Niels-Clayton/self-tuning-buck-converter/Reports/Final Report/appendix/source_code.tex

\chapter{Source Code} \label{A:code}

\section*{Single Header Libraries: Hardware Drivers} \label{A:headers}

\subsection*{adc.h} \label{A:adc_code}
\lstinputlisting{code/adc.h} 

\newpage
\subsection*{pid.h} \label{A:pid_code}
\lstinputlisting{code/pid.h}

\newpage
\subsection*{pwm.h} \label{A:pwm_code}
\lstinputlisting{code/pwm.h}

\newpage
\section*{Application Code} \label{A:application_code}

\subsection*{buck\_converter.h}\label{A:buck_code}
\lstinputlisting{code/buck_converter.h} 

\newpage
\subsection*{buck\_converter.c}
\lstinputlisting{code/buck_coverter.c} 

\newpage
\subsection*{main.c} \label{A:main_code}
\lstinputlisting{code/main.c}
