Niels-Clayton/self-tuning-buck-converter/self-tuning-buck-converter/Peak Detector/Evaluation/error/final_design_error.pdf

Final Design
Measured Output Error vs Switching Frequency

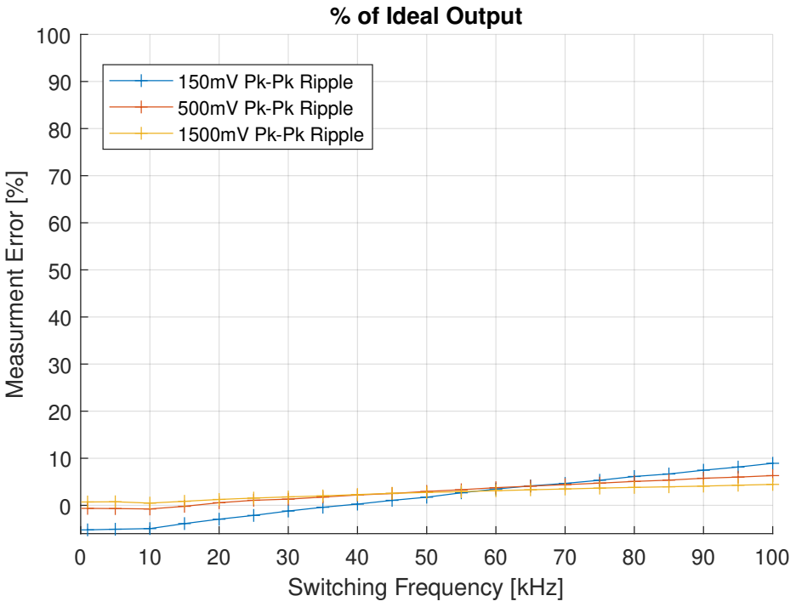
[picture p42: figure]
Switching Frequency [kHz]; Measurment Error [%]; % of Ideal Output; 150mV Pk-Pk Ripple 500mV Pk-Pk Ripple 1500mV Pk-Pk Ripple
