Niels-Clayton/self-tuning-buck-converter/docs/Planning/Proposal_Gantt_Chart.xlsx

ENGR489 Gantt Chart
Niels Clayton - Self Tuning Buck Converter
Month | March |  | April |  |  |  | May |  |  |  |  | June |  |  |  | July |  |  |  | August |  |  |  |  | September |  |  |  | October
Week Beginning | 22 | 29 | 5 | 12 | 19 | 26 | 3 | 10 | 17 | 24 | 31 | 7 | 14 | 21 | 28 | 5 | 12 | 19 | 26 | 2 | 9 | 16 | 23 | 30 | 6 | 13 | 20 | 27 | 4 | 11
Phase 1 - Research & Setup
Literature Review
Component Selection/Purchase
Buck Converter Dev Board Design
Phase 2 - Design
PWM Generation Testing & Evaluation
Feedback Sensor Testing & Evaluation
Complete Hardware Selection
Phase 3 - Implementation
Controller Implementation
Final PCB Design
Evaluation
Reports
Preliminary Report Writing
Presentation Preperation
Final Report Writing
Deadlines |  |  |  |  |  |  |  |  | Prelim. Report - 24/05 |  |  |  |  |  | Mid Year Break |  |  |  |  |  |  |  |  | Draft Final Report - 03/09 |  |  |  |  | Final Report - 08/10
 |  |  |  |  |  |  |  |  |  |  |  |  |  |  |  |  |  |  |  |  |  |  |  |  |  |  |  |  |  | Presentations - 15/10
