Niels-Clayton/self-tuning-buck-converter/Reports/Final Report/Figures/background/Duty_cycle.png

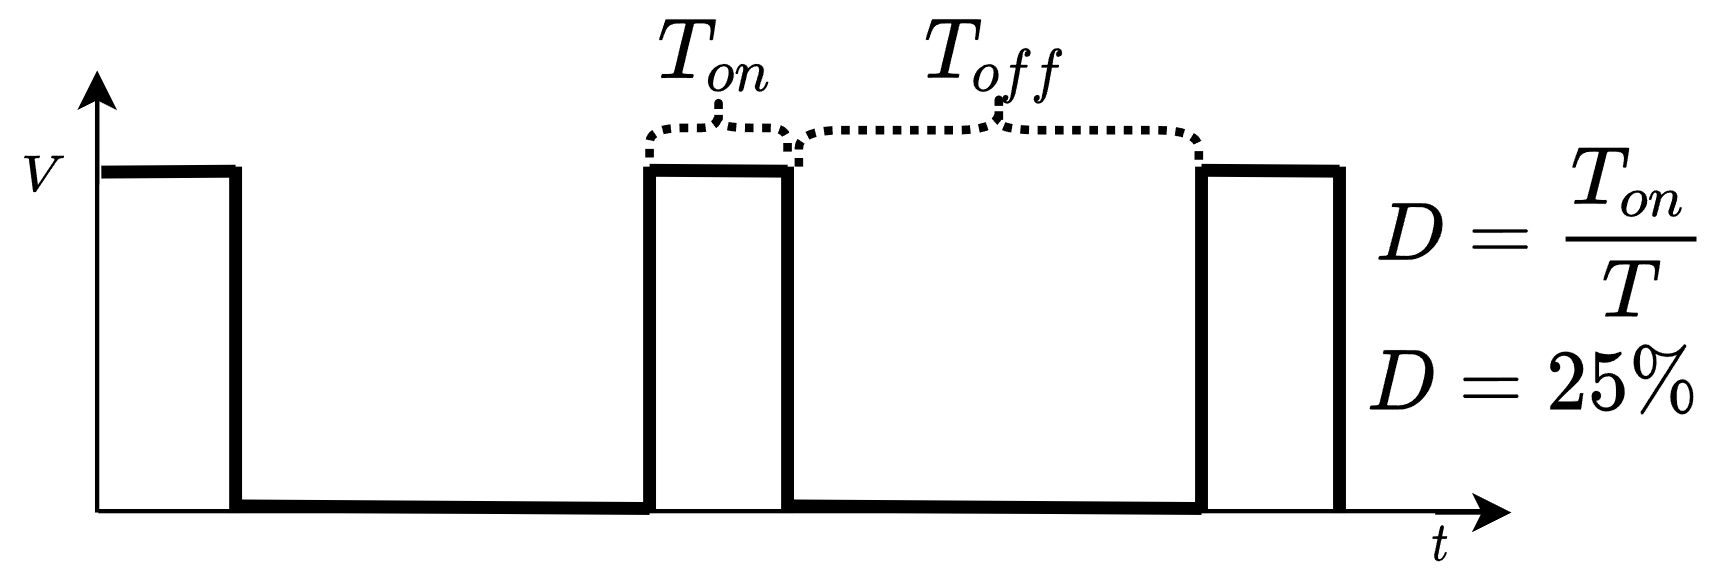
Reports/Final Report/Figures/background/Duty_cycle.png
