Niels-Clayton/self-tuning-buck-converter/Reports/Final Report/Figures/pwm/analog/analogue_PWM_ltspice_1k.png

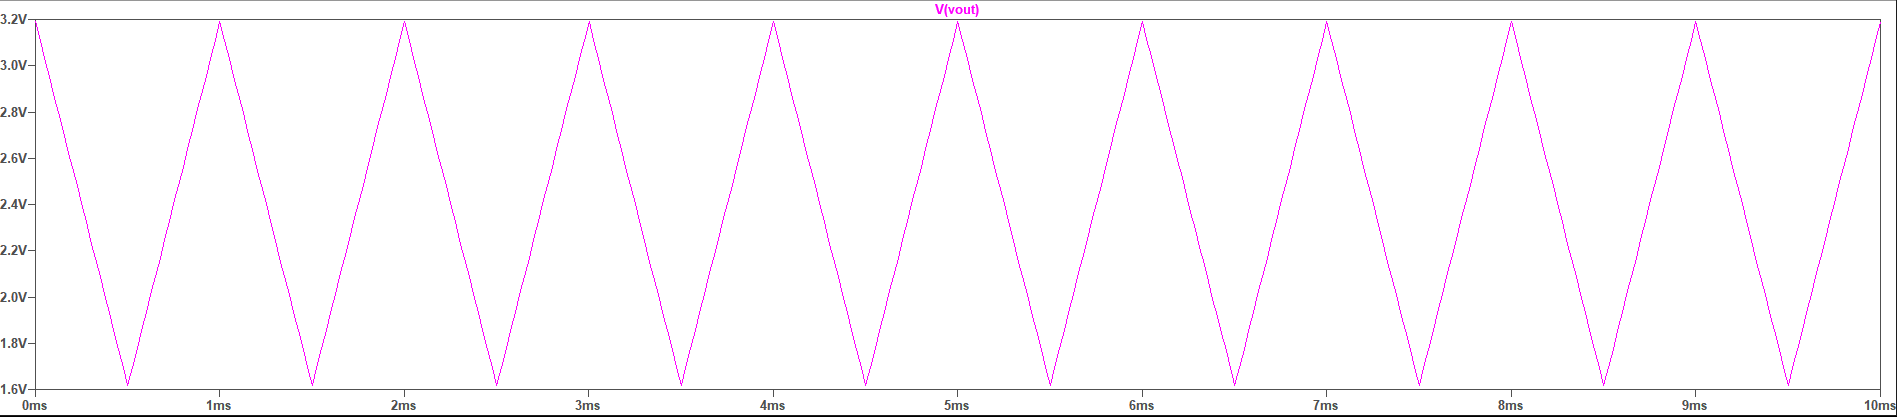
Reports/Final Report/Figures/pwm/analog/analogue_PWM_ltspice_1k.png
