Niels-Clayton/self-tuning-buck-converter/Reports/Final Report/Figures/pwm/duty/1kHz_75Duty.JPG

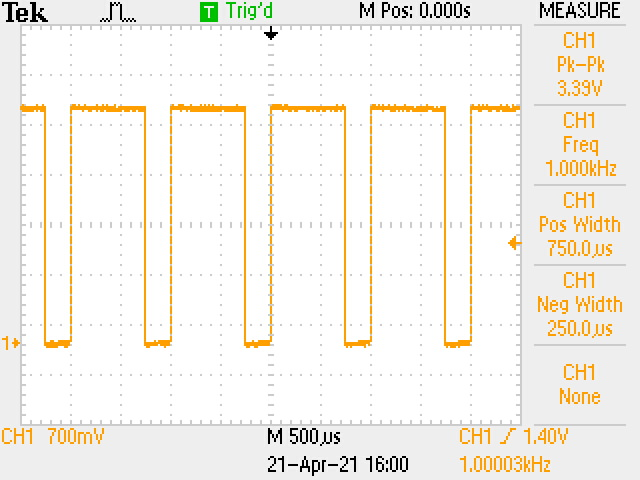
Reports/Final Report/Figures/pwm/duty/1kHz_75Duty.JPG
