Niels-Clayton/self-tuning-buck-converter/Reports/Final Report/Figures/pwm/duty/100kHz_50Duty.JPG

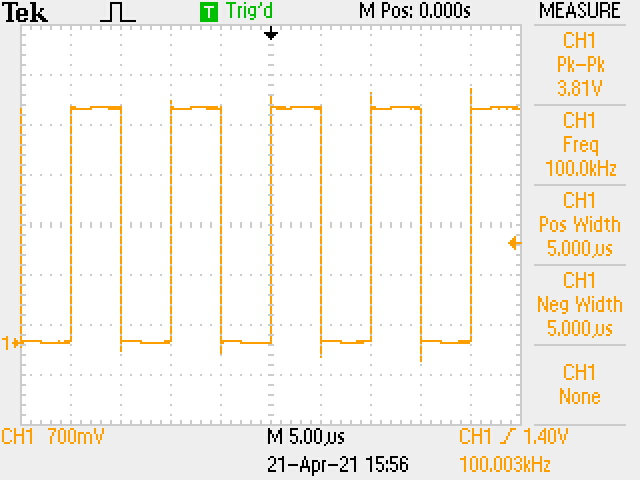
Reports/Final Report/Figures/pwm/duty/100kHz_50Duty.JPG
