Niels-Clayton/self-tuning-buck-converter/Reports/Final Report/Figures/pwm/duty/100kHz_75Duty.JPG

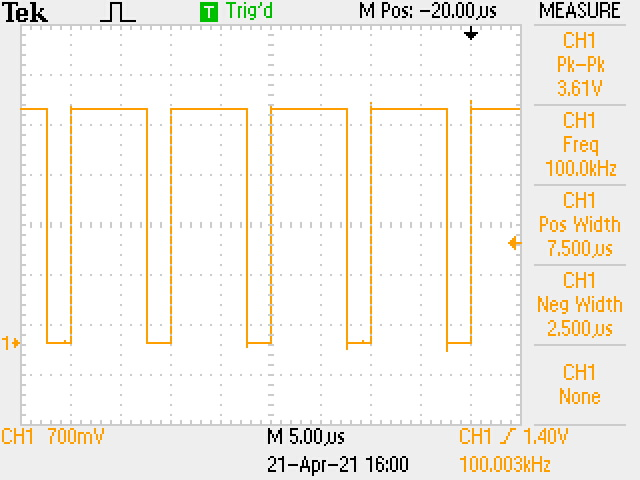
Reports/Final Report/Figures/pwm/duty/100kHz_75Duty.JPG
