Niels-Clayton/self-tuning-buck-converter/Reports/Final Report/Figures/control/step_response/voltage_control_3-10-0.PNG

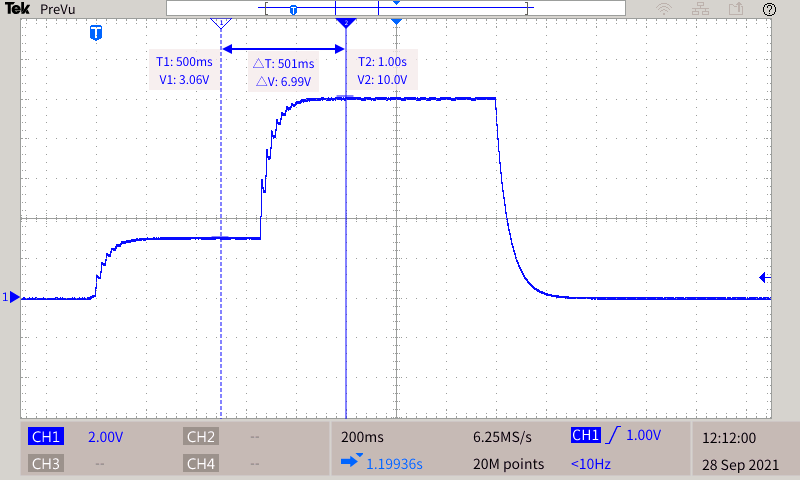
Reports/Final Report/Figures/control/step_response/voltage_control_3-10-0.PNG
