Niels-Clayton/self-tuning-buck-converter/self-tuning-buck-converter/Peak Detector/Evaluation/Peak Detector Evaluation.csv

Peak Detection Accuracy Comparison |  |  |  |  |  |  | Peak Detection Accuracy Comparison |  |  |  |  |  |  | Peak Detection Accuracy Comparison
Voltage pk-pk (mV) |  | 150 |  |  |  |  | Voltage pk-pk (mV) |  | 500 |  |  |  |  | Voltage pk-pk (mV) |  | 1500
Voltage Peak (mV) |  | 75 |  |  |  |  | Voltage Peak (mV) |  | 250 |  |  |  |  | Voltage Peak (mV) |  | 750
Voltage Refrence (mV) |  | 5999.90 |  |  |  |  | Voltage Refrence (mV) |  | 6002.20 |  |  |  |  | Voltage Refrence (mV) |  | 6001.70
Frequency (kHz) | V_out new (mV) | new error (mV) | new % error | V_out old (mV) | old error (mV) | old % error | Frequency (kHz) | V_out new (mV) | new error (mV) | new % error | V_out old (mV) | old error (mV) | old % error | Frequency (kHz) | V_out new (mV) | new error (mV) | new % error | V_out old (mV) | old error (mV) | old % error
1 | 6078.80 | -3.90 | -5.2 | 6071.50 | 3.40 | 4.533333333 | 1 | 6253.80 | -1.60 | -0.64 | 6245.20 | 7.00 | 2.8 | 1 | 6746.30 | 5.40 | 0.72 | 6736.70 | 15.00 | 2
5 | 6078.70 | -3.80 | -5.066666667 | 6069.10 | 5.80 | 7.733333333 | 5 | 6253.90 | -1.70 | -0.68 | 6237.20 | 15.00 | 6 | 5 | 6746.00 | 5.70 | 0.76 | 6722.00 | 29.70 | 3.96
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
