Niels-Clayton/self-tuning-buck-converter/self-tuning-buck-converter/PWM/evaluation/pwm_duty.csv

Actual | Target
0.996094 | 0.000000
0.996094 | 0.001953
0.000000 | 0.003906
0.500000 | 0.005859
0.500000 | 0.007812
0.750000 | 0.009766
0.800000 | 0.011719
0.800000 | 0.013672
0.857143 | 0.015625
0.875000 | 0.017578
0.875000 | 0.019531
0.900000 | 0.021484
0.900000 | 0.023438
0.916667 | 0.025391
0.923077 | 0.027344
0.923077 | 0.029297
0.933333 | 0.031250
0.937500 | 0.033203
0.937500 | 0.035156
0.944444 | 0.037109
0.947368 | 0.039062
0.947368 | 0.041016
0.952381 | 0.042969
0.954545 | 0.044922
0.954545 | 0.046875
0.958333 | 0.048828
0.958333 | 0.050781
0.961538 | 0.052734
0.962963 | 0.054688
0.962963 | 0.056641
0.965517 | 0.058594
0.966667 | 0.060547
0.966667 | 0.062500
0.968750 | 0.064453
0.969697 | 0.066406
0.969697 | 0.068359
0.971429 | 0.070312
0.971429 | 0.072266
0.972973 | 0.074219
0.973684 | 0.076172
0.973684 | 0.078125
0.975000 | 0.080078
0.975610 | 0.082031
0.975610 | 0.083984
0.976744 | 0.085938
0.977273 | 0.087891
0.977273 | 0.089844
0.978261 | 0.091797
0.978261 | 0.093750
0.979167 | 0.095703
0.979592 | 0.097656
0.979592 | 0.099609
0.980392 | 0.101562
0.980769 | 0.103516
0.980769 | 0.105469
0.981481 | 0.107422
0.981818 | 0.109375
0.981818 | 0.111328
0.982456 | 0.113281
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
