Niels-Clayton/self-tuning-buck-converter/self-tuning-buck-converter/PWM/evaluation/pwm_frequency.csv

Actual | Target | error | 62
1000 | 1000 | 0
1001 | 1001 | 0
1002 | 1002 | 0
1003 | 1003 | 0
1004 | 1004 | 0
1005 | 1005 | 0
1006 | 1006 | 0
1007 | 1007 | 0
1008 | 1008 | 0
1009 | 1009 | 0
1010 | 1010 | 0
1011 | 1011 | 0
1012 | 1012 | 0
1013 | 1013 | 0
1014 | 1014 | 0
1015 | 1015 | 0
1016 | 1016 | 0
1017 | 1017 | 0
1018 | 1018 | 0
1019 | 1019 | 0
1020 | 1020 | 0
1021 | 1021 | 0
1022 | 1022 | 0
1023 | 1023 | 0
1024 | 1024 | 0
1025 | 1025 | 0
1026 | 1026 | 0
1027 | 1027 | 0
1028 | 1028 | 0
1029 | 1029 | 0
1030 | 1030 | 0
1031 | 1031 | 0
1032 | 1032 | 0
1033 | 1033 | 0
1034 | 1034 | 0
1035 | 1035 | 0
1036 | 1036 | 0
1037 | 1037 | 0
1038 | 1038 | 0
1039 | 1039 | 0
1040 | 1040 | 0
1041 | 1041 | 0
1042 | 1042 | 0
1043 | 1043 | 0
1044 | 1044 | 0
1045 | 1045 | 0
1046 | 1046 | 0
1047 | 1047 | 0
1048 | 1048 | 0
1049 | 1049 | 0
1050 | 1050 | 0
1051 | 1051 | 0
1052 | 1052 | 0
1053 | 1053 | 0
1054 | 1054 | 0
1055 | 1055 | 0
1056 | 1056 | 0
1057 | 1057 | 0
1058 | 1058 | 0
1059 | 1059 | 0
1060 | 1060 | 0
1061 | 1061 | 0
1062 | 1062 | 0
1063 | 1063 | 0
1064 | 1064 | 0
1065 | 1065 | 0
1066 | 1066 | 0
1067 | 1067 | 0
1068 | 1068 | 0
1069 | 1069 | 0
1070 | 1070 | 0
1071 | 1071 | 0
1072 | 1072 | 0
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
