Niels-Clayton/self-tuning-buck-converter/self-tuning-buck-converter/Voltage_control_system/images/buck_closedloop_continuious.png

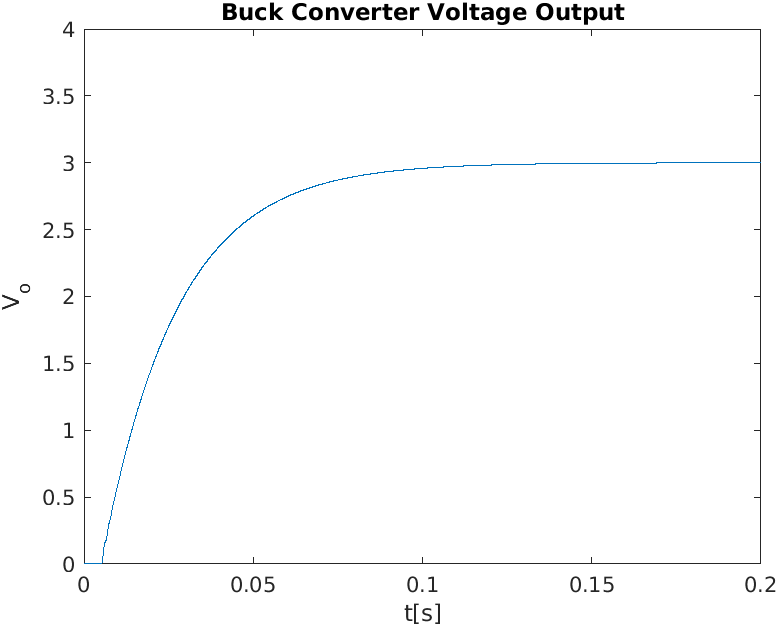
self-tuning-buck-converter/Voltage_control_system/images/buck_closedloop_continuious.png
