Niels-Clayton/self-tuning-buck-converter/self-tuning-buck-converter/Voltage_control_system/images/buck_controlled_discrete.png

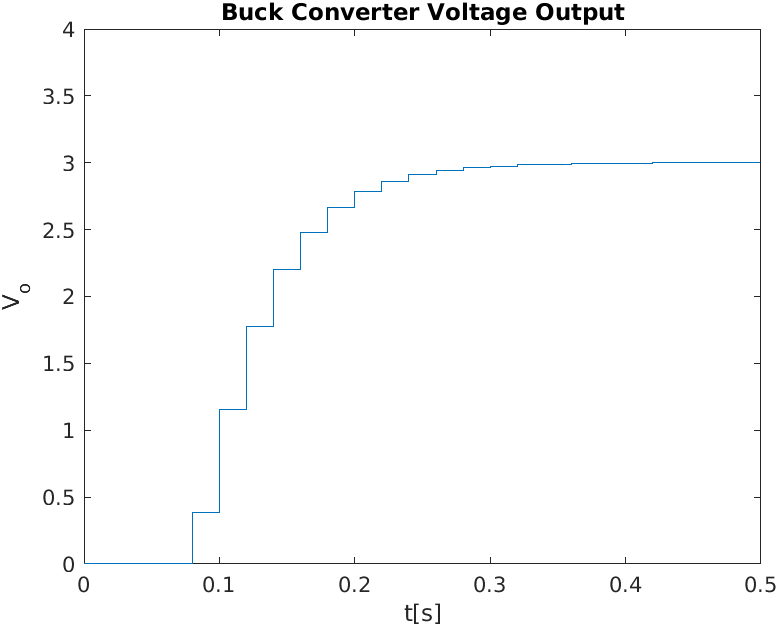
self-tuning-buck-converter/Voltage_control_system/images/buck_controlled_discrete.png
