Niels-Clayton/self-tuning-buck-converter/self-tuning-buck-converter/Voltage_control_system/images/buck_openloop_continuious.png

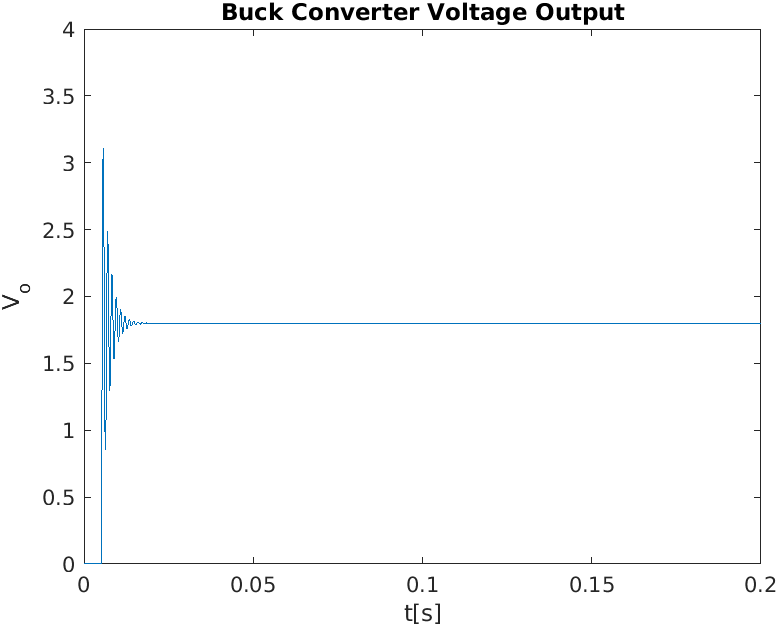
self-tuning-buck-converter/Voltage_control_system/images/buck_openloop_continuious.png
