Niels-Clayton/self-tuning-buck-converter/self-tuning-buck-converter/Voltage_control_system/images/closed_loop_voltage_out.png

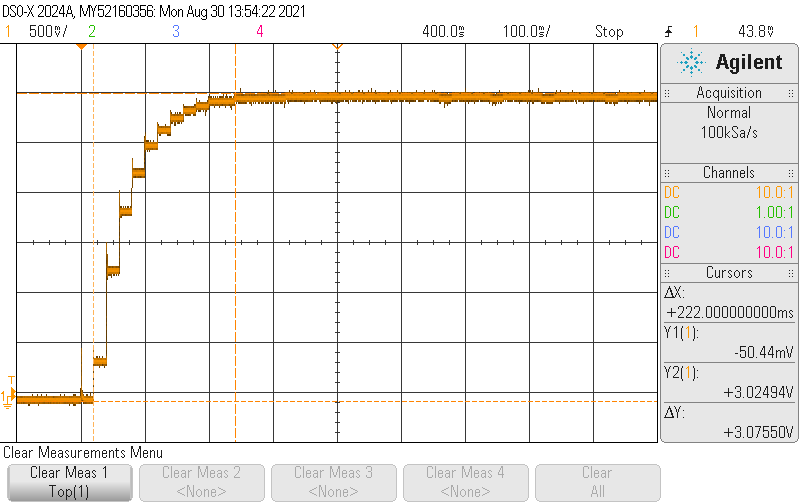
self-tuning-buck-converter/Voltage_control_system/images/closed_loop_voltage_out.png
