Niels-Clayton/self-tuning-buck-converter/self-tuning-buck-converter/Voltage_control_system/images/open_loop_votage_out.png

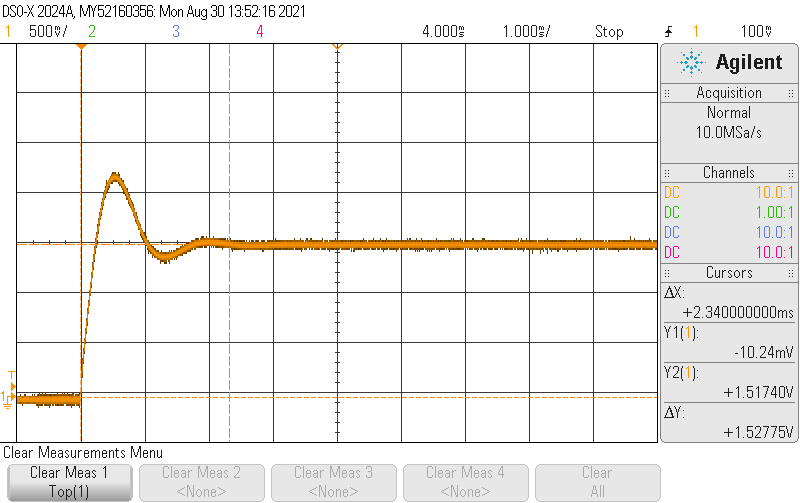
self-tuning-buck-converter/Voltage_control_system/images/open_loop_votage_out.png
