Niels-Clayton/self-tuning-buck-converter/Reports/Final Report/Figures/current_sense/schematic/average_current.pdf

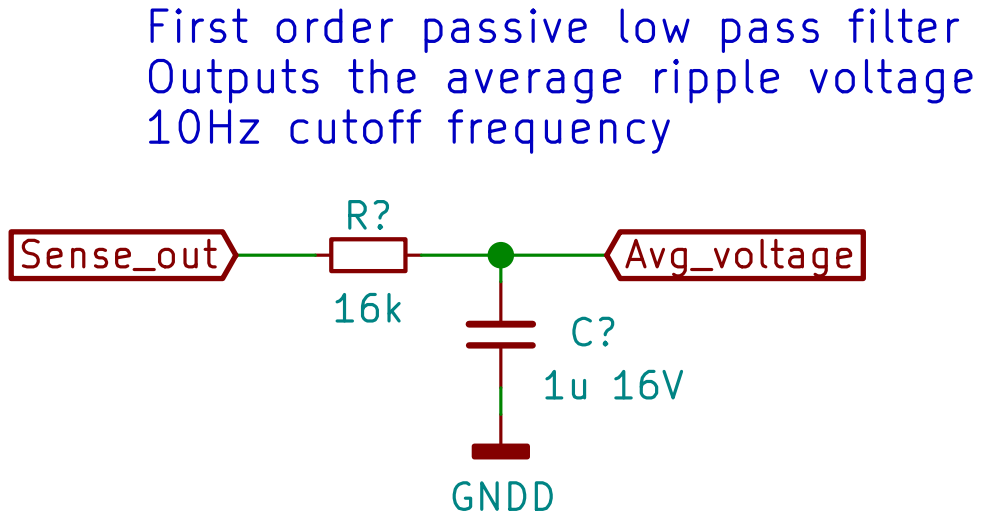
[picture p83: page 1]
GNDD; Avg_voltage V_ref; Pk_voltage; Sense_out Pk_voltage V_ref V_ref V_ref Sense_ripple; V_ref

First order passive low pass filter
Outputs the average ripple voltage
10Hz cutoff frequency

Id: 2/2 Title: File: test.sch Sheet: /test/ D? DIODE R?
