Niels-Clayton/self-tuning-buck-converter/Reports/Final Report/Figures/current_sense/schematic/precision_rectifier_schematic.pdf

3 | U?A OPAMP R?
3 | U?A OPAMP R?

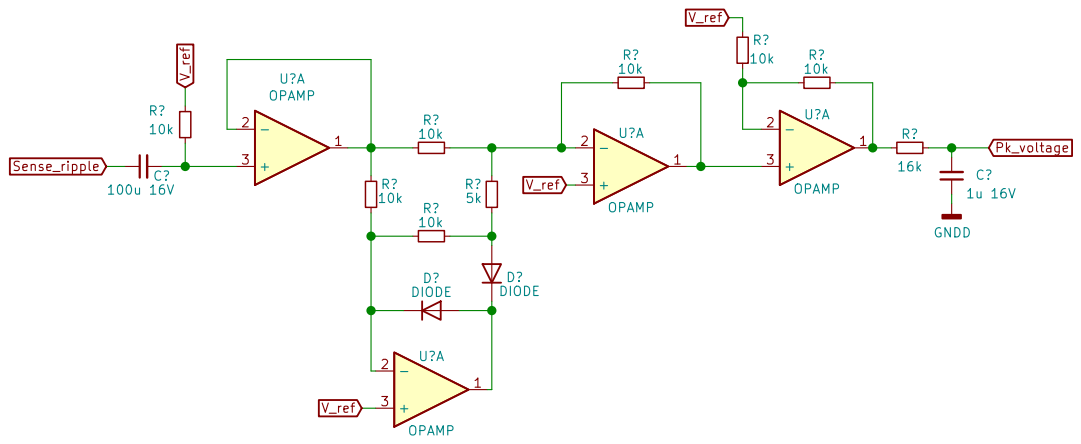
[picture p84: page 1]
U?A OPAMP; 5k D? DIODE; 16k GNDD; Pk_voltage; Sense_out Pk_voltage V_ref V_ref V_ref Sense_ripple; V_ref

Id: 2/2 Title: File: test.sch Sheet: /test/ D? DIODE R?
