Niels-Clayton/self-tuning-buck-converter/Reports/Final Report/Figures/current_sense/schematic/sample_and_hold_schematic.pdf

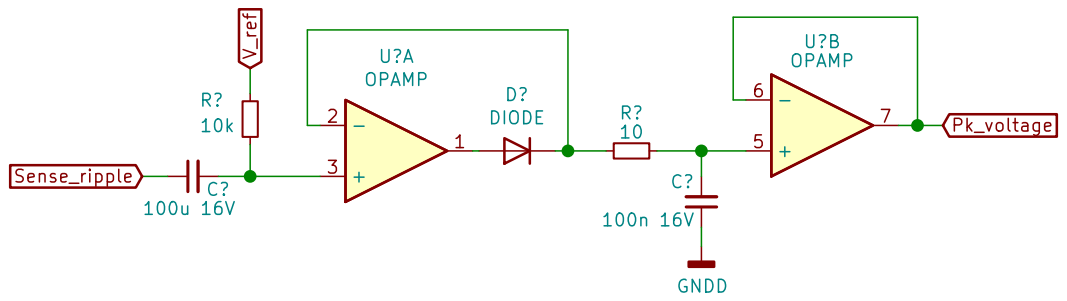
[picture p85: page 1]
D? DIODE; U?A OPAMP; GNDD; 7 U?B OPAMP; Avg_voltage V_ref; Sense_ripple; Pk_voltage; Sense_out Pk_voltage V_ref V_ref V_ref Sense_ripple; V_ref

Id: 2/2 Title: File: test.sch Sheet: /test/ D? DIODE R?
