Niels-Clayton/self-tuning-buck-converter/Reports/Final Report/Figures/pwm/duty/duty_range.pdf

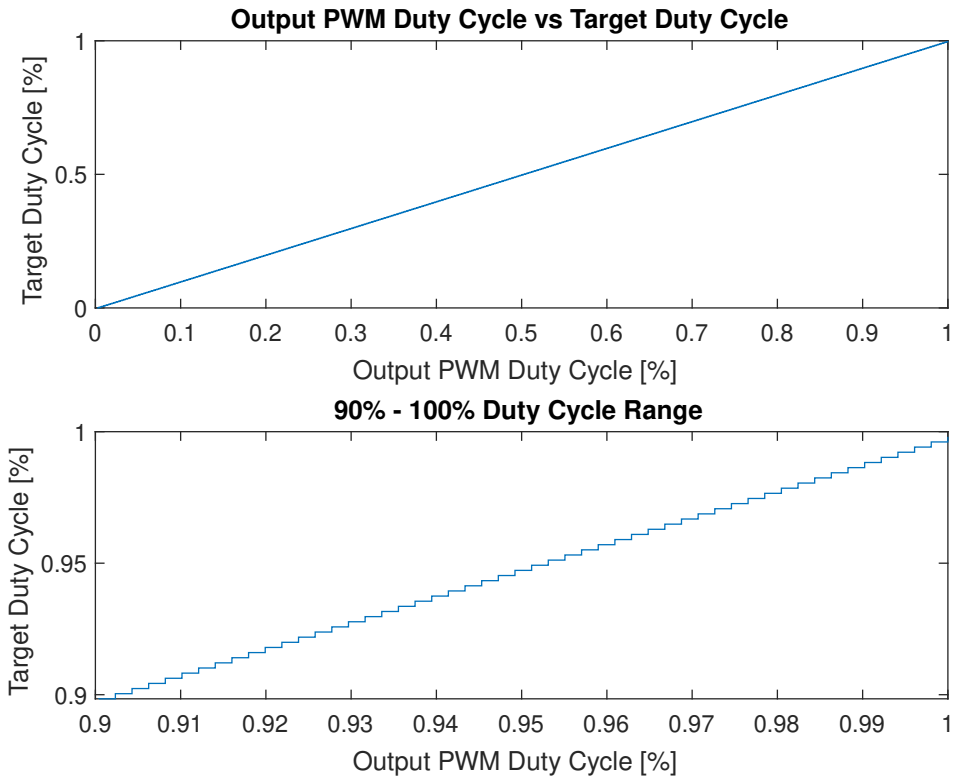
[picture p86: page 1]

Output PWM Duty Cycle vs Target Duty Cycle

Target Duty Cycle [%]

Output PWM Duty Cycle [%]
90% - 100% Duty Cycle Range
