Niels-Clayton/self-tuning-buck-converter/Reports/Final Report/Figures/pwm/frequency/frequency_error.pdf

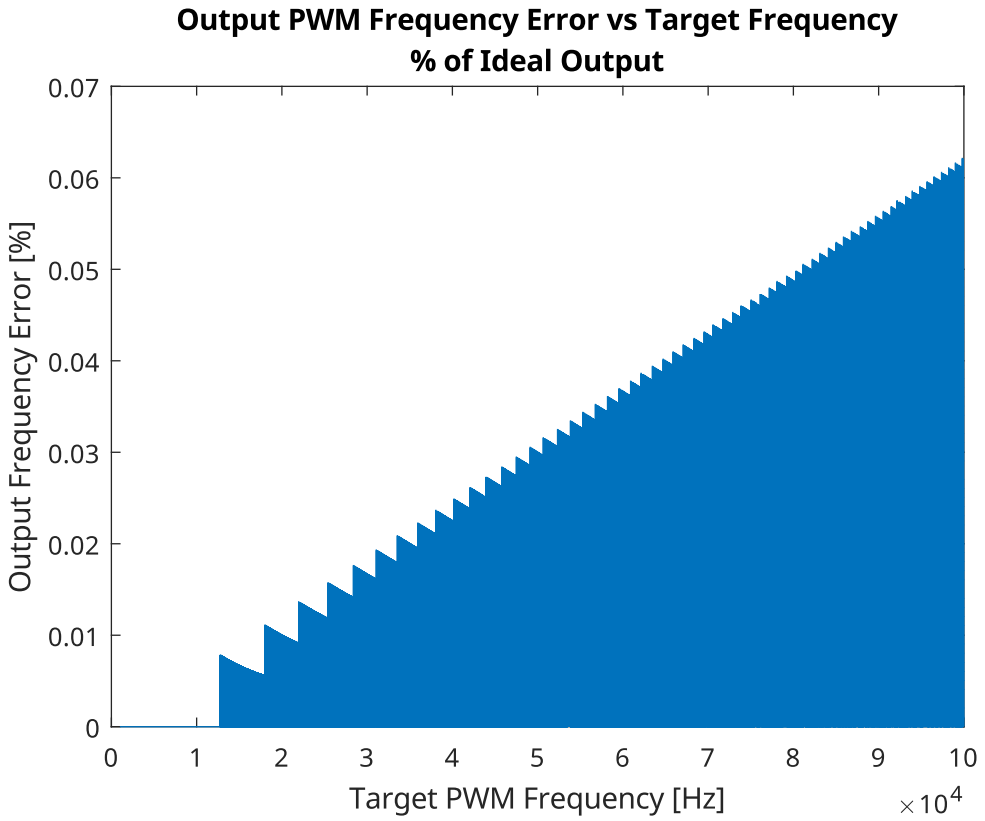
[picture p87: page 1]
