Niels-Clayton/self-tuning-buck-converter/Reports/Final Report/Figures/pwm/frequency/frequency_range.pdf

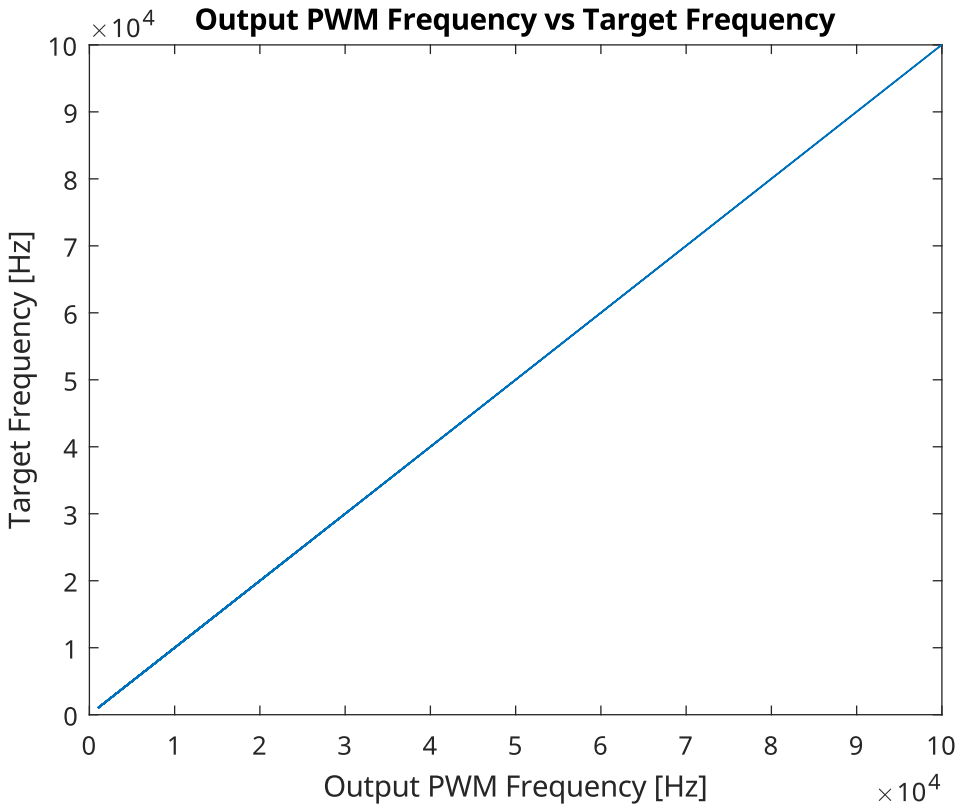
[picture p88: page 1]
