Niels-Clayton/self-tuning-buck-converter/self-tuning-buck-converter/Precision Rectifier/precision_rectifier.asc

C1: cap; 100n
C3: cap; 1n
C6: cap; 1n
C7: cap; 1µ
D1: diode; 1N4148
D2: diode; 1N4148
D4: diode; 1N4148
R1: res; 10
R2: res; 820k
R3: res; 1k
R4: res; 10k
R5: res; 10k
R6: res; 10k
R8: res; 1Meg
R9: res; 1k
R10: res; 1Meg
R11: res; 1k
R12: res; 1k
R13: res; 1k
R14: res; 500
R15: res; 1k
R16: res; 16k
U1: LTC6244
U3: LTC6244
U4: OP27
U5: LTC6244
U6: LTC6244
U7: LTC6244
U9: LTC6244
V1: voltage; 12
V3: voltage; PULSE(0 1 0 0.002m 0.008m 1e-10 0.01m)
Named nets: 0, VCC, V_ref, ripple_1, Precision_Rectifier, Sample_and_hold, V_ripple
.tran 0 0.0504s 0.0502s 0.02
