Niels-Clayton/self-tuning-buck-converter/self-tuning-buck-converter/Peak Detector/Improved Peak Detector/improved_peak_detector.asc

C6: cap; 100µ
C7: cap; 10n
D4: schottky; 5082-2804
R1: res; 10
R2: res; 10k
R3: res; 100k
R4: res; 1Meg
R9: res; 100k
U1: LTC6244
U2: opamp2; LM7322
U3: opamp2; LM7322
V1: voltage; SINE(0 0.5 10K 80u 0 0 3)
V2: voltage; SINE(0 0.7 100k 500u 0 0 30)
V3: voltage; 5
Named nets: IN, 0, +V, V_ref, OUT
.model 5082-2804 D(Is=22n Rs=25 N=1.08 Cjo=1.6p M=0.5 Eg=.69 Xti=2 Iave=100m Vpk=75 mfg=Avago type=Schottky)
.tran 0 2m 0 0.000001
.include lib/LMH6658.lib
.include lib/LM7322.lib
.include lib/TL972.lib
