Niels-Clayton/self-tuning-buck-converter/self-tuning-buck-converter/design/Peak Detector/peak_detector.asc

C3: cap; 1n
C4: cap; 10n
D3: diode; 1N4148
D4: diode; 1N4148
R3: res; 1Meg
R4: res; 10k
R5: res; 10k
R6: res; 10k
R7: res; 10k
U4: OP27
U5: OP27
U6: OP27
U7: OP27
V1: voltage; 12
V2: voltage; SINE(0 0.4 100k 0 0 0)
V3: voltage; PULSE(-0.4 0.4 0 0.002m 0.008m 1e-10 0.01m)
Named nets: 0, VCC, ripple, V_ref, ripple_1
.tran 0 0.104s 0.102s 0.02
