Niels-Clayton/self-tuning-buck-converter/self-tuning-buck-converter/Peak Detector/Analog Devices Peak Detector/LTC6244_PeakDetector_Improved.asc

C1: cap; 2.5n
C2: cap; 10µ
D1: schottky; BAT54
D2: schottky; 5082-2804
M1: nmos
R1: res; 10K
R2: res; 80
R4: res; 10Meg
R5: res; 10K
R6: res; 10K
R7: res; 1K
R8: res; 10K
U1: LTC6244
U2: LTC6244
V1: voltage; SINE(0 0.1 100K 80u 0 0 3)
V2: voltage; SINE(0 8 50k 200u 0 0 10)
V3: voltage; 12
V5: voltage; PULSE(0 8.5 130u 1e-9 1e-9 50u 1 1)
Named nets: 0, IN, +V, OUT
.model 5082-2804 D(Is=22n Rs=25 N=1.08 Cjo=1.6p M=0.5 Eg=.69 Xti=2 Iave=100m Vpk=75 mfg=Avago type=Schottky)
.tran 1m
LTC6244 - Dual 50MHz, Low Noise, Rail-to-Rail, CMOS Op Amp
Improved Peak Detector
Note:
  If the simulation model is not found please update with the "Sync Release" command from the "Tools" menu.
  It remains the customer's responsibility to verify proper and reliable operation in the actual application.
  Component substitution and printed circuit board layout may significantly affect circuit performance or reliability.
  Contact your local sales representative for assistance. This circuit is distributed to customers only for use with LTC parts.
  Copyright © 2016 Linear Technology Inc. All rights reserved.
