Niels-Clayton/self-tuning-buck-converter/self-tuning-buck-converter/design/Precision Rectifier/Draft1.asc

C2: cap; 47p
C3: cap; 1n
C4: cap; 15.9µ
C6: cap; 1n
C7: cap; 15.9µ
D1: diode; 1N4148
D2: diode; 1N4148
D3: diode; 1N4148
D4: diode; 1N4148
R1: res; 1k
R2: res; 1k
R4: res; 10k
R5: res; 10k
R6: res; 1k
R7: res; 1k
R8: res; 1Meg
R10: res; 1Meg
R11: res; 1k
R12: res; 1k
R13: res; 1k
R14: res; 500
R15: res; 1k
R16: res; 1k
U1: OP27
U2: OP27
U3: OP27
U4: OP27
U5: OP27
U6: OP27
U7: OP27
U8: OP27
V1: voltage; 12
V2: voltage; SINE(0 0.4 100k 0 0 0)
V3: voltage; PULSE(-0.4 0.4 0 0.002m 0.008m 1e-10 0.01m)
Named nets: 0, VCC, ripple, V_ref, ripple_1
.tran 0 0.1004s 0.1002s 0.02
