Niels-Clayton/self-tuning-buck-converter/self-tuning-buck-converter/PWM/analog/analogue-PWM-integrator.asc

C1: cap; 1.59n
PWM_Source: voltage; PULSE(2 3 0 0.1u 0.1u {period/2} {period})
R1: res; 100k
R2: res; 100Meg
R3: res; 10k
R4: res; 10k
U2: UniversalOpamp2
VCC: voltage; 5
Named nets: 0, V+, vref, Vin, Vout
.param period=1/100k
.tran 0 {period*1000} {period*990} {period/100}
